NWSpitfire/Ender-3-Stealthburner-Edition/Software/heaters.cfg

#All Heaters/Extruders configs

[extruder]
step_pin: PB3
dir_pin: PB4
enable_pin: !PC3
microsteps: 16
gear_ratio: 50:17
rotation_distance: 22.4521616 #sb calculated
nozzle_diameter: 0.400
filament_diameter: 1.750
heater_pin: PA1
sensor_type: EPCOS 100K B57560G104F
sensor_pin: PC5
#control: pid
#pid_Kp: 21.527
#pid_Ki: 1.063
#pid_Kd: 108.982
min_temp: 0
max_temp: 300
#pressure_advance: 0.0425
pressure_advance: 0.025
#pressure_advance_smooth_time: 0.040


[heater_bed]
heater_pin: PA2
sensor_type: EPCOS 100K B57560G104F
sensor_pin: PC4
#control: pid
#pid_Kp: 54.027
#pid_Ki: 0.770
#pid_Kd: 948.182
min_temp: 0
max_temp: 115
